frescogo/frescogo/slides/avericao.png

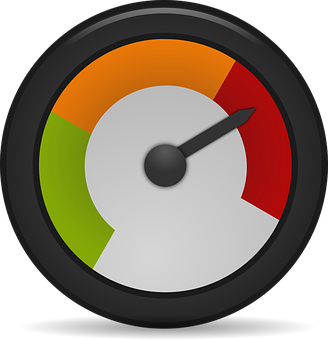
slides/avericao.png
