frescogo/frescogo/slides/frescogo-2020-10-11_19_55_07-Rhayani-Duboly-placar.png

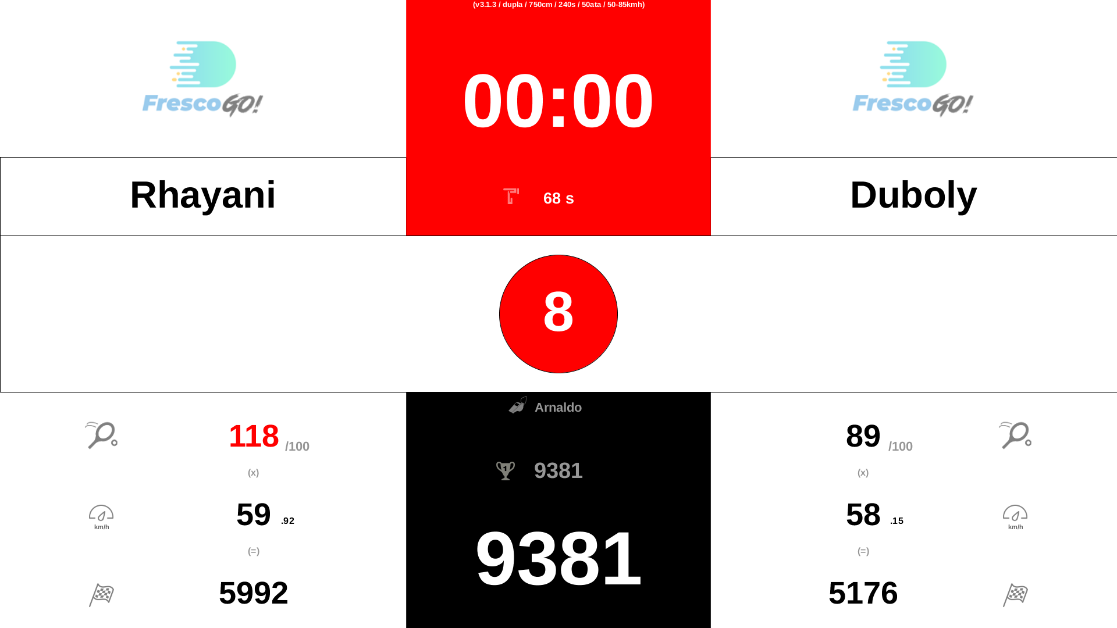
slides/frescogo-2020-10-11_19_55_07-Rhayani-Duboly-placar.png
