frescogo/frescogo/slides/heart-white.png

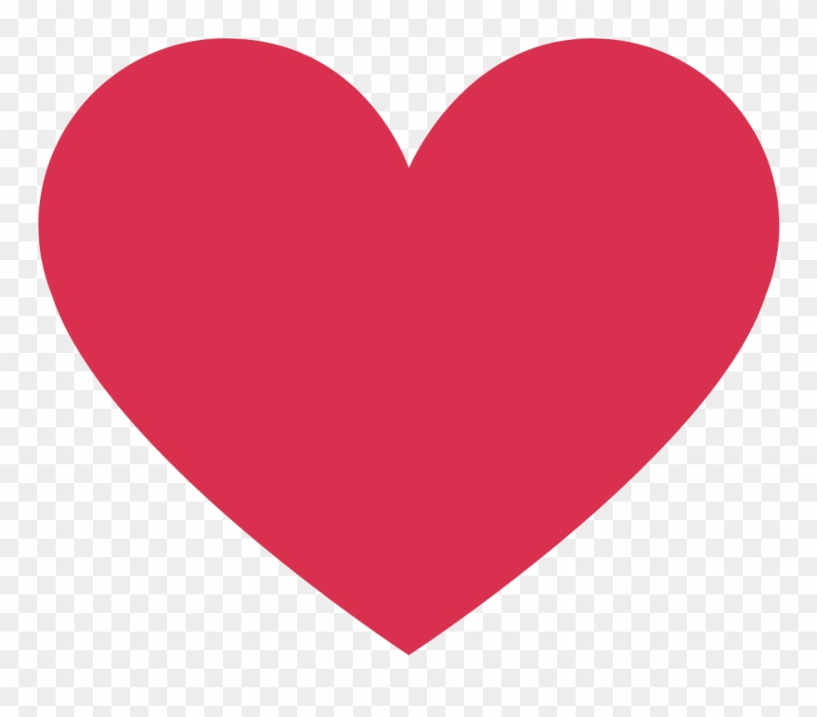
slides/heart-white.png
