frescogo/frescogo/slides/regras.jpg

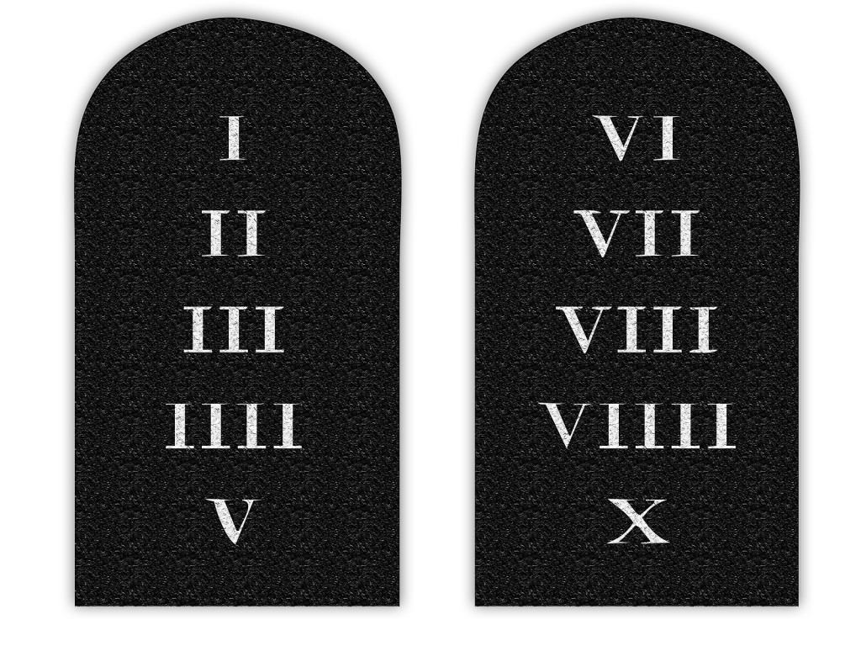
slides/regras.jpg
