frescogo/frescogo/slides/regras.png

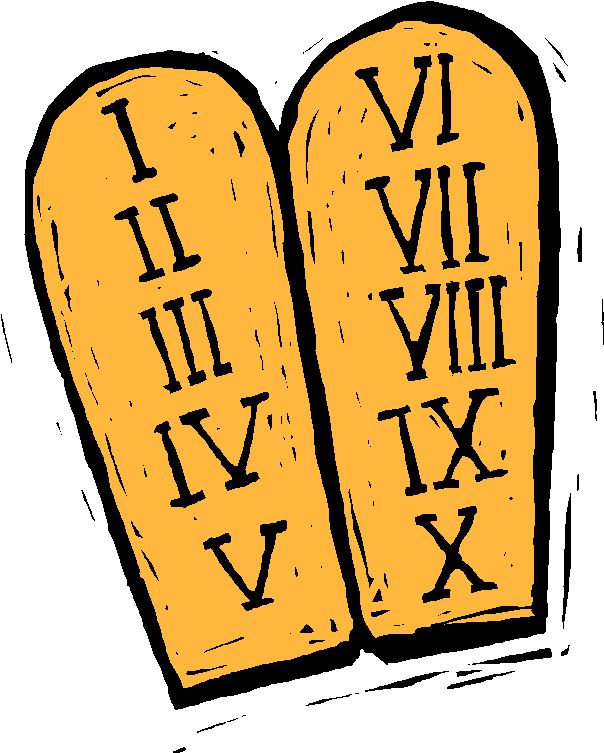
slides/regras.png
