frescogo/frescogo/slides/scale.png

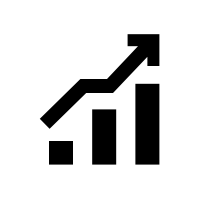
slides/scale.png
